erebus-labs/blocks-o-code/docs/Test Plans/Hardware-3.pdf

Test Case Name: | Programmer Breakout Connectivity | Test ID: | ABC-Hardware-03
Description: | Verify connectivity of external programmer breakout. | Type: | Black box

Tester Information:
Name of Tester: | | | Date:
Harware Ver: | | BlockBoard v2.2 | Time:
Setup: | | A fully populated programmer breakout. A digital multimeter will be required.
| Action | Expected Result | Pass | Fail | Comments
1 | Measure between header pin 1 and connector pin 3. | Electrical connection present.
2 | Measure between header pin 2 and connector pin 7. | Electrical connection present.
3 | Measure between header pin 3 and connector pin 8. | Electrical connection present.
4 | Measure between header pin 4 and connector pin 9. | Electrical connection present.
5 | Measure between header pin 5 and connector pin 1. | Electrical connection present.
6 | Measure between header pin 6 and connector pin 6. | Electrical connection present.

Overall test result

Ste

p

Test Writer: Daniel Frister
