erebus-labs/blocks-o-code/images/BlockBoard2.png

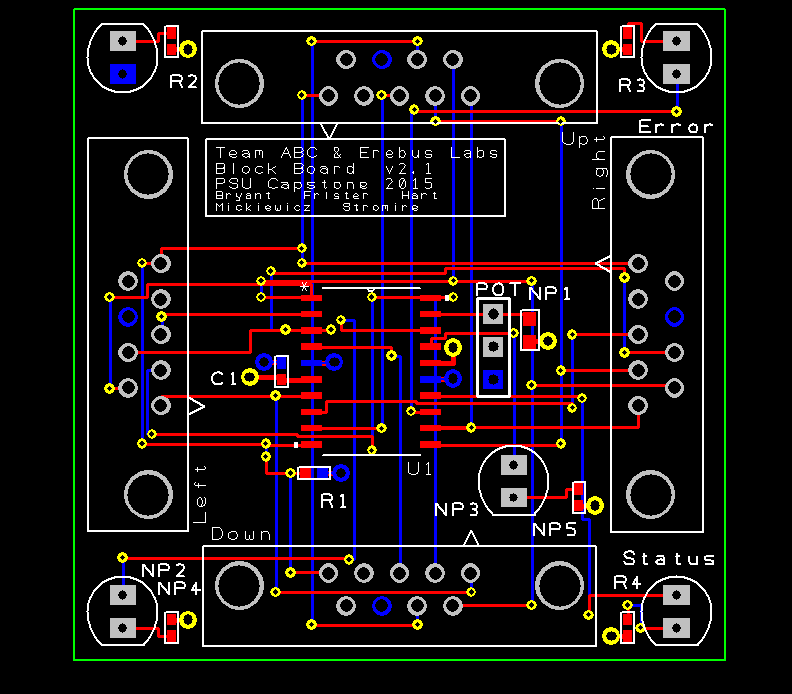
images/BlockBoard2.png
