erebus-labs/blocks-o-code/images/blockFace_with_wheel.png

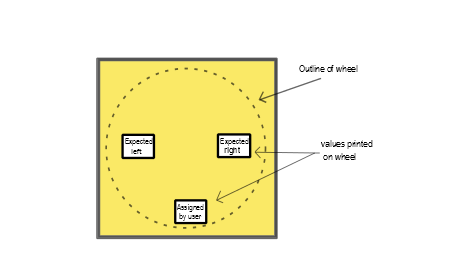
images/blockFace_with_wheel.png
