erebus-labs/blocks-o-code/images/osh.png

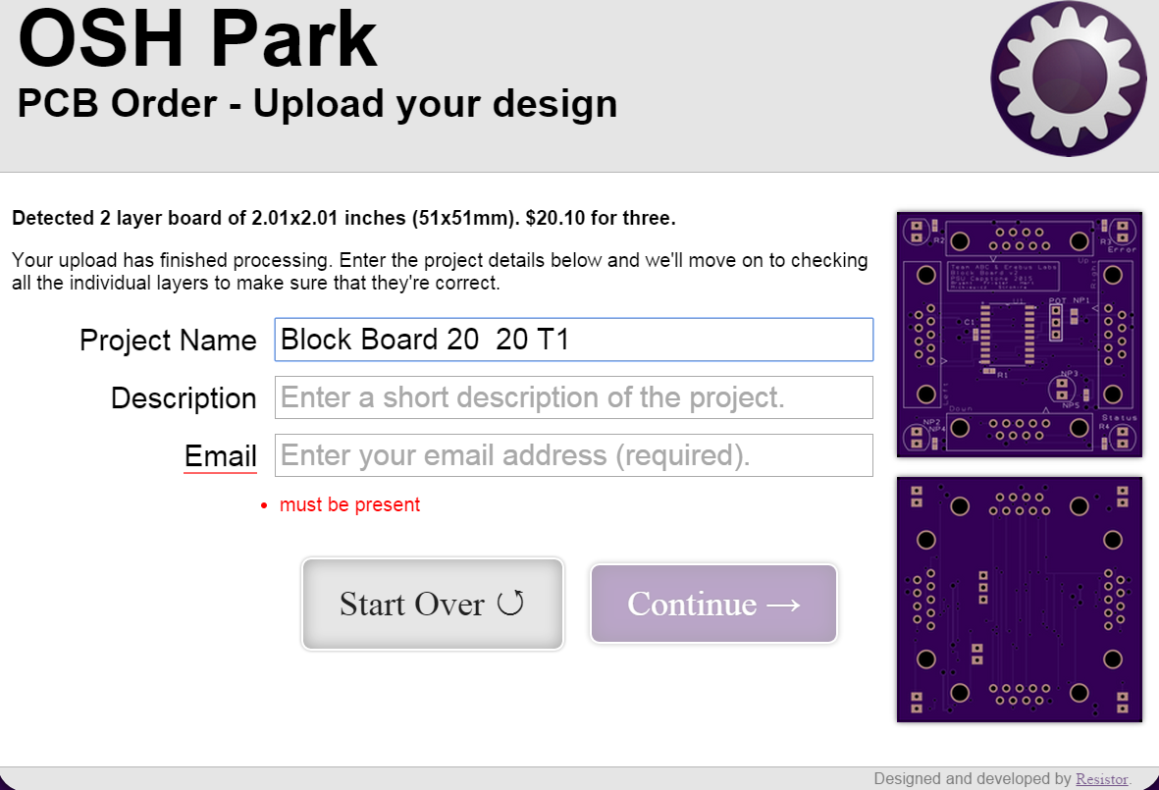
images/osh.png
