erebus-labs/blocks-o-code/docs/pdfs/BlockBoard - Schematic.pdf

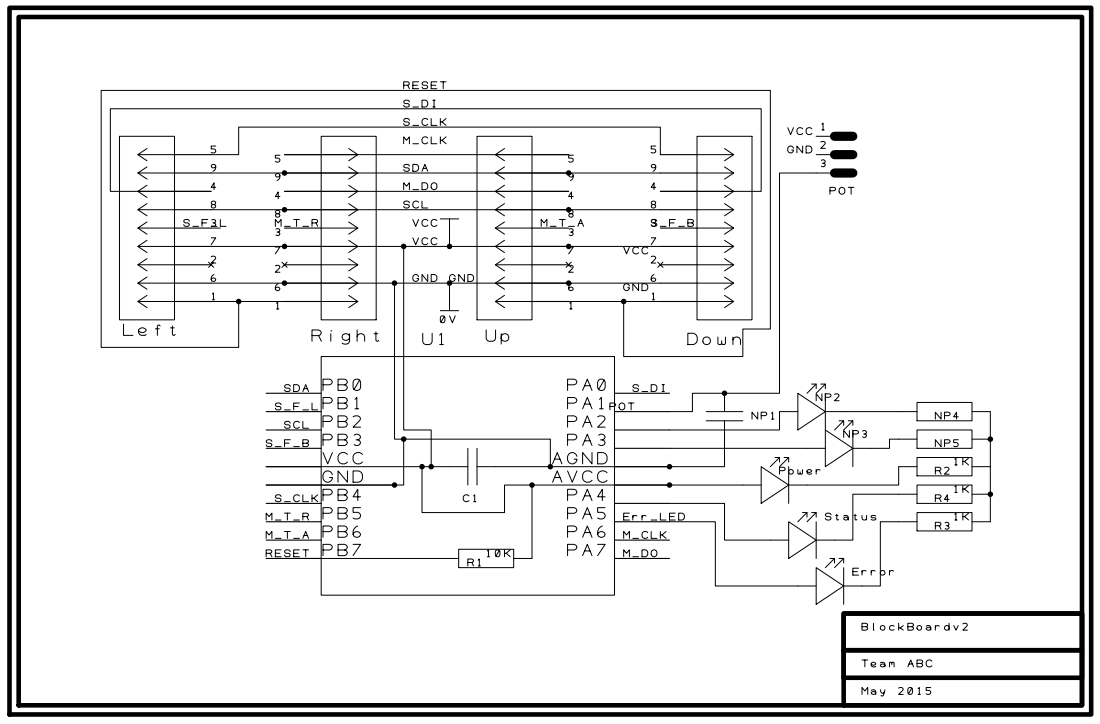
[picture p45: page 1]
