erebus-labs/blocks-o-code/docs/pdfs/BlockBoard - PCB.pdf

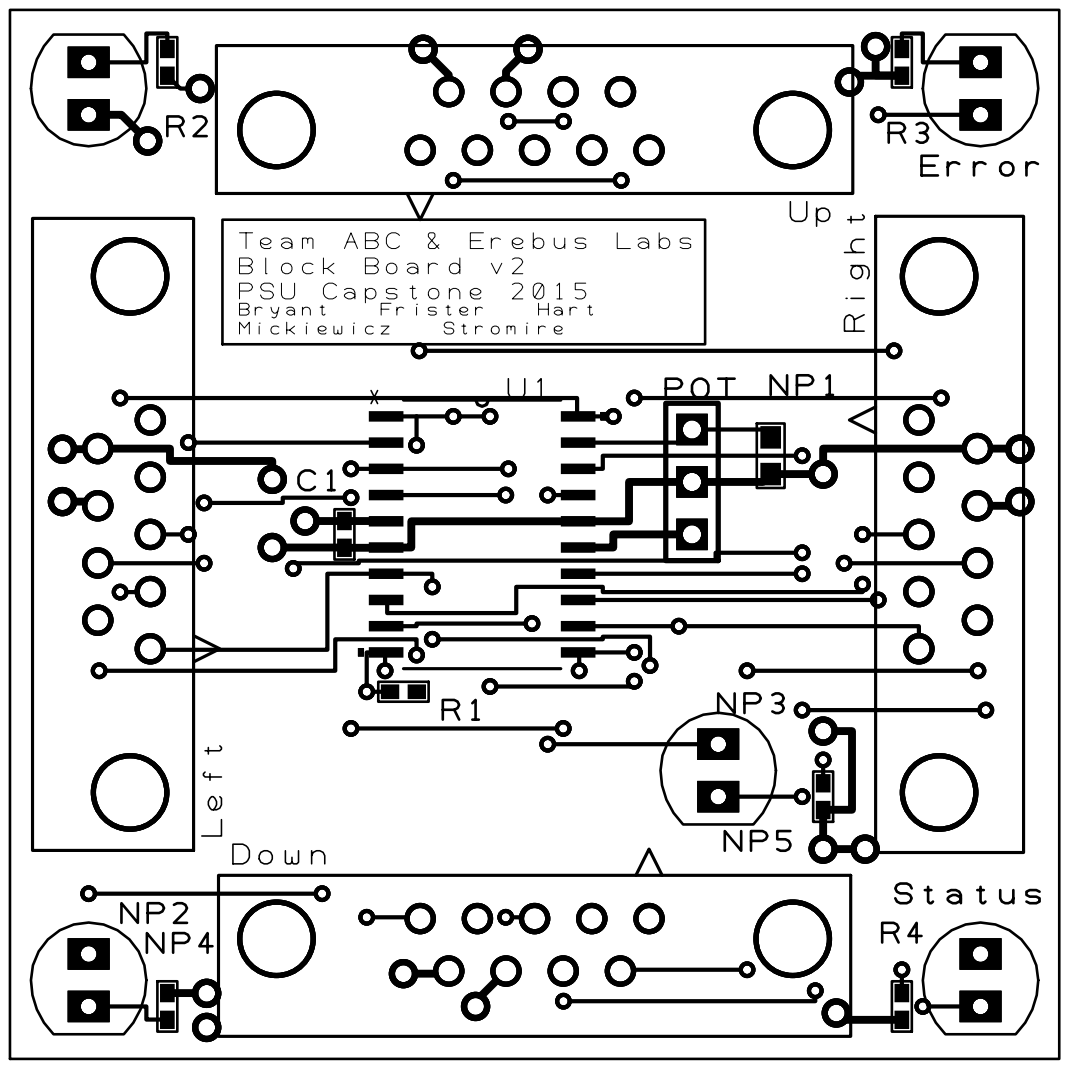
[picture p46: page 1]
