erebus-labs/blocks-o-code/docs/pdfs/ABlockofCodeSchedGantt.pdf

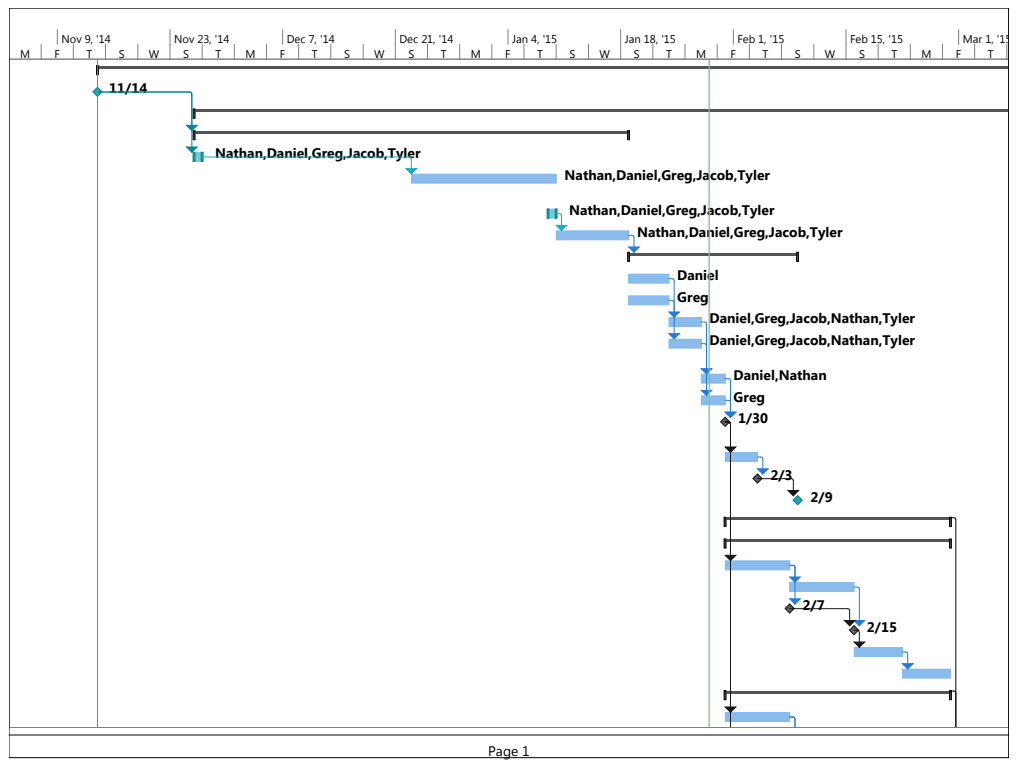
[picture p47: page 1]
Daniel,Nathan; Greg; Nov 9, '14; Nov 23, '14; Dec 7, '14; Dec 21, '14; Jan 4, '15; Jan 18, '15; Feb 1, '15; Feb 15, '15; Mar 1, '15; Page 1

Nathan,Daniel,Greg,Jacob,Tyler

Daniel
Greg
Daniel,Greg,Jacob,Nathan,Tyler

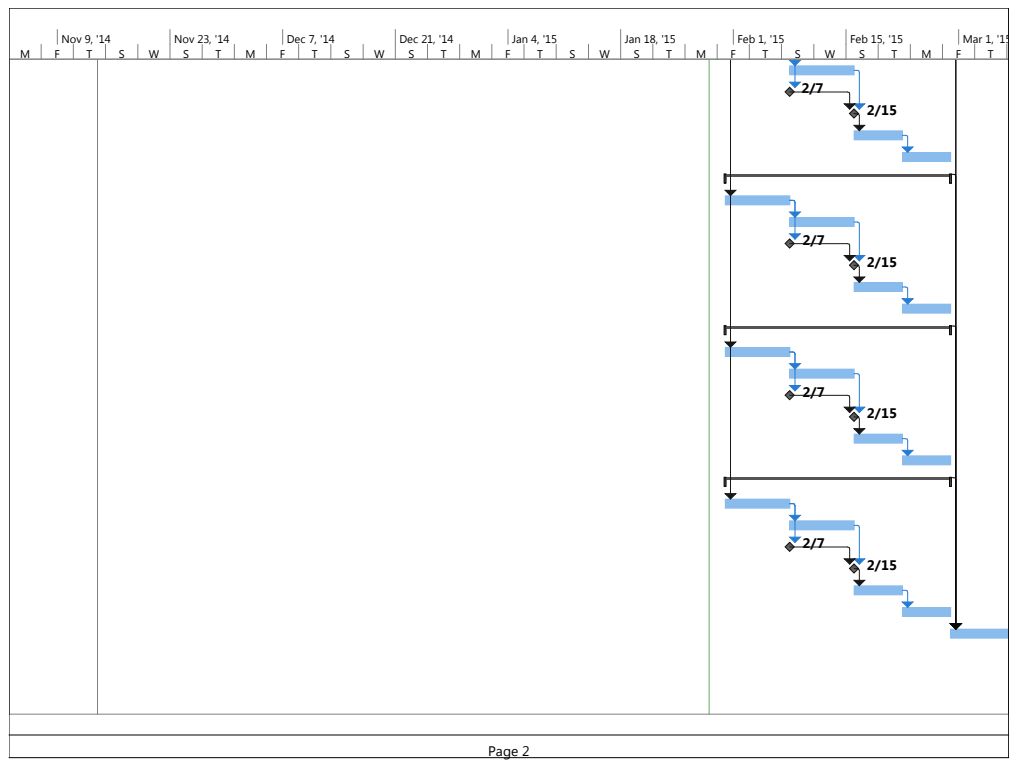
[picture p48: page 2]
Nov 9, '14; Nov 23, '14; Dec 7, '14; Dec 21, '14; Jan 4, '15; Jan 18, '15; Feb 1, '15; Feb 15, '15; Mar 1, '15; Page 2

M | F | T | S | W | S | T | M | F | T | S | W | S | T | M | F | T | S | W | S | T | M | F | T | S | W | S | T | M | F | T
Nov 9, '14 | Nov 23, '14 | Dec 7, '14 | Dec 21, '14 | Jan 4, '15 | Jan 18, '15 | Feb 1, '15 | Feb 15, '15 | Mar 1, '15

### Page 3

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

### Page 4

S | W | S | T | M | F | T | S | W | S | T | M | F | T | S | W | S | T | M | F | T | S | W | S | T | M | F | T | S | W | S
Mar 15, '15 | Mar 29, '15 | Apr 12, '15 | Apr 26, '15 | May 10, '15 | May 24, '15 | Jun 7, '15 | Jun 21, '15 | Jul 5, '15

### Page 5

### Daniel,Greg,Jacob,Nathan,Tyler

### Daniel,Greg,Jacob,Nathan,Tyler

### Greg

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

### Page 6

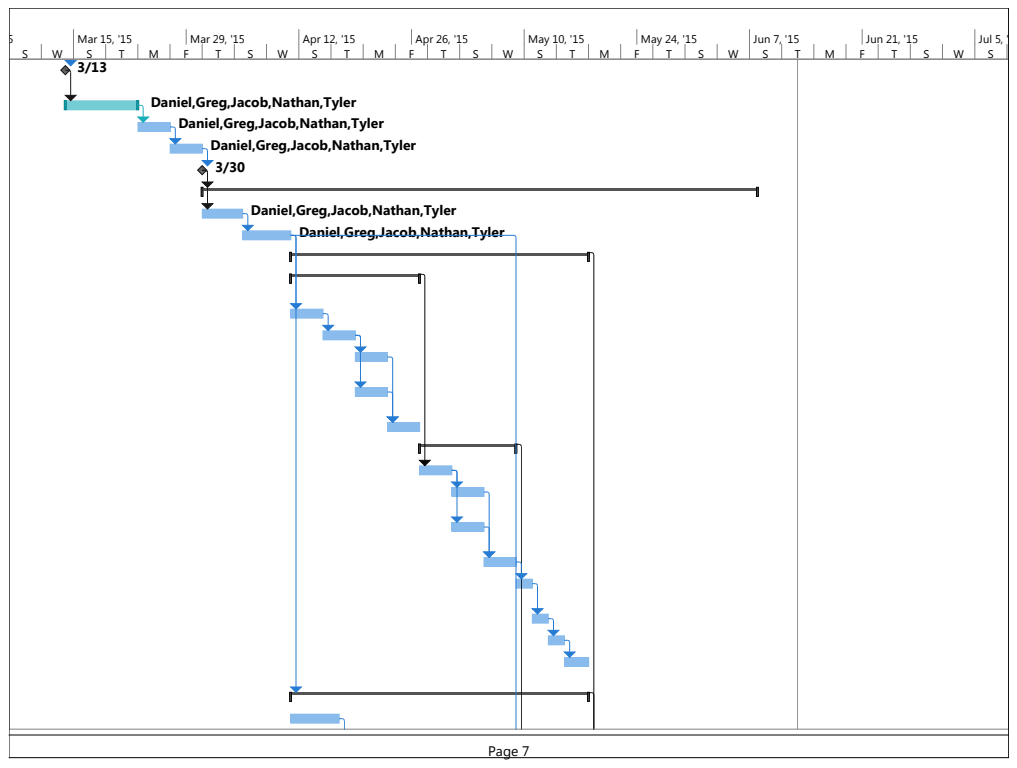
[picture p49: page 7]
Mar 15, '15; Mar 29, '15; Apr 12, '15; Apr 26, '15; May 10, '15; May 24, '15; Jun 7, '15; Jun 21, '15; Jul 5, '15; Page 7

Daniel,Greg,Jacob,Nathan,Tyler

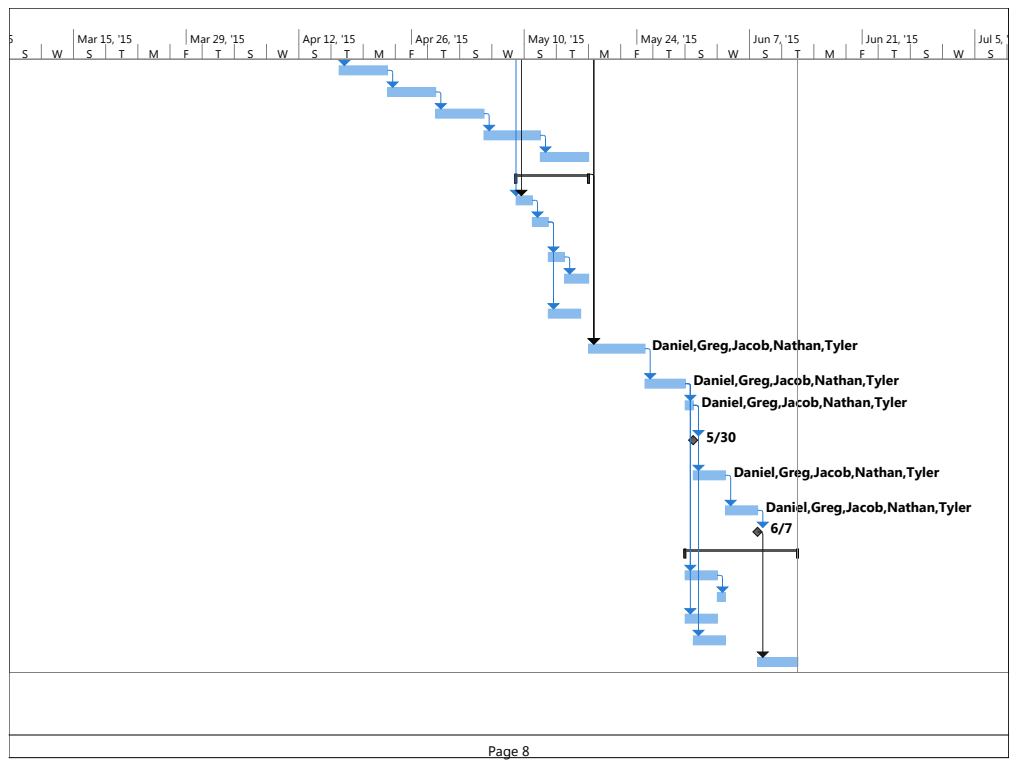
[picture p50: page 8]
Mar 15, '15; Mar 29, '15; Apr 12, '15; Apr 26, '15; May 10, '15; May 24, '15; Jun 7, '15; Jun 21, '15; Jul 5, '15; Page 8

Daniel,Greg,Jacob,Nathan,Tyler
