erebus-labs/blocks-o-code/dev/uC/LEDs/main.c

//
// Integrated Daisy Chain and I2C for A Block of Code project
//

#include "abc_daisy.h"
#include "i2c_slave.h"

static void initIO(void);
static void startupSequence(void);

int main(void) {
	
	// initialization
	initIO();
	startupSequence();
	startupSequence();
	_delay_ms(100);
	
	// spin until position received from connected block (or BBB)
	uint8_t addr = waitForVector();
	
	// add offset to show up in BBB scan
	addr += 10;
	
	// assign received vector to i2c initialization
	setup_i2c(addr, 36, 0, 3);
	sei();
	
	// continuously poll i2c for commands
	while (loop_i2c()) {
		_delay_ms(200);
		TOGGLE_STATUS;
	}
	return 0; // never reached
}


void initIO(void) {
	// set output pins
#ifdef MCU_2313
	DDRA |= _BV(PD0);
	DDRA |= _BV(PD1);
	DDRA |= _BV(PD2);
	DDRA |= _BV(PD3);
	DDRA |= _BV(STATUS_LED);
	DDRA |= _BV(ERROR_LED);
#endif
#ifdef MCU_461
	DDRA |= _BV(PA2);
	DDRA |= _BV(PA3);
	DDRA |= _BV(PA4);
	DDRA |= _BV(PA5);
	DDRA |= _BV(STATUS_LED);
	DDRA |= _BV(ERROR_LED);
#endif
}

void startupSequence(void) {
#ifdef MCU_2313
	for(int i = 0; i < 4; ++i){
		_delay_ms(25);
		PORTD |= _BV(PD0 + i);
	}
	for(int i = 0; i < 4; ++i){
		_delay_ms(25);
		PORTD &= ~_BV(PD0 + i);
	}
#endif
#ifdef MCU_461
	PORTA |= _BV(PA2);
	_delay_ms(25);
	PORTA |= _BV(PA3);
	_delay_ms(25);
	PORTA |= _BV(PA4);
	_delay_ms(25);
	PORTA |= _BV(PA5);
	_delay_ms(25);
	PORTA &= ~_BV(PA2);
	_delay_ms(25);
	PORTA &= ~_BV(PA3);
	_delay_ms(25);
	PORTA &= ~_BV(PA4);
	_delay_ms(25);
	PORTA &= ~_BV(PA5);
	_delay_ms(25);
	PORTA &= 0b11000000;
#endif
}
