erebus-labs/blocks-o-code/src/controller/abc/interpreter/src/globals.h

/****************************************
****         A Block of Code         ****
*****************************************

Parsing Emulator for A Block of Code
* Greg's proposal for syntax/symantics

(C)2014-2015 Erubus Labs
* For internal use only (subject to change)

****************************************/

/// \file globals.h
/// \brief A nice place to put stuff

#ifndef ABC_GLOBALS_H
#define ABC_GLOBALS_H

/* Macros ******************************/
#ifdef PRINTDEBUGINFO
#define DEBUG(...) fprintf(stderr, ">>> " __VA_ARGS__);
#else
#define DEBUG(...) ;
#endif

/* Globals *****************************/
extern double globals[];
extern FILE* g_source_file;
extern int g_interactive_quit;

void g_reset_globals();

#endif
