erebus-labs/blocks-o-code/dev/BBB/abc_global.py

# abc_global.py

from Adafruit_I2C import Adafruit_I2C

class Commands:
    (
    ReadData,
    SendVertical,
    SendHorizontal,
    StatusLedOn,
    StatusLedBlink,
    StatusLedOff,
    ErrorLedOn,
    ErrorLedBlink,
    ErrorLedOff,
    Reset,
    AuxiliaryRead
    ) = range(11)


class ABC_Global_Bus(object):
    """docstring for ABC_Global_Bus"""
    def __init__(self):
        super(ABC_Global_Bus, self).__init__()
        f = open('/sys/devices/bone_capemgr.9/slots', 'w')
        f.write('BB-I2C1')
        try:
            f.close()
        except IOError as e:
            if e.errno != 17:
                raise

    def formatAddress(self, x, y):
        if int(x) > 7 or int(y) > 15:
            return -1
        return (int(x) & 7) | ((int(y) & 15) << 3)

    # returns function value stored in the block's function register
    def serviceCommand(self, x, y, i2c_busnum=2, register=0):
        return Adafruit_I2C(self.formatAddress(x, y), busnum=i2c_busnum).readU8(register)

    def readData(self, x, y, i2c_busnum=2):
        return self.serviceCommand(x, y, i2c_busnum, Commands.ReadData)

    def sendVertical(self, x, y, i2c_busnum=2):
        return self.serviceCommand(x, y, i2c_busnum, Commands.SendVertical)

    def sendHorizontal(self, x, y, i2c_busnum=2):
        return self.serviceCommand(x, y, i2c_busnum, Commands.SendHorizontal)

    def statusLedOn(self, x, y, i2c_busnum=2):
        return self.serviceCommand(x, y, i2c_busnum, Commands.StatusLedOn)

    def statusLedBlink(self, x, y, i2c_busnum=2):
        return self.serviceCommand(x, y, i2c_busnum, Commands.StatusLedBlink)

    def statusLedOff(self, x, y, i2c_busnum=2):
        return self.serviceCommand(x, y, i2c_busnum, Commands.StatusLedOff)

    def errorLedOn(self, x, y, i2c_busnum=2):
        return self.serviceCommand(x, y, i2c_busnum, Commands.ErrorLedOn)

    def errorLedBlink(self, x, y, i2c_busnum=2):
        return self.serviceCommand(x, y, i2c_busnum, Commands.ErrorLedBlink)

    def errorLedOff(self, x, y, i2c_busnum=2):
        return self.serviceCommand(x, y, i2c_busnum, Commands.ErrorLedOff)

    def reset(self, x, y, i2c_busnum=2):
        return self.serviceCommand(x, y, i2c_busnum, Commands.Reset)

    def auxiliaryRead(self, x, y, i2c_busnum=2):
        return self.serviceCommand(x, y, i2c_busnum, Commands.AuxiliaryRead)
