erebus-labs/blocks-o-code/src/controller/abc/proto_lex.py

#!/usr/bin/python

from abc_lexer import ABC_Lexer
import time
import sys


delay = 1.25

continuous = False
debug = False
stderr = True
if len(sys.argv)>1:
	if '-c' in sys.argv:
		continuous = True
	if '-debug' in sys.argv:
		debug = True
	if '-E' in sys.argv:
		stderr = False

lex = ABC_Lexer(debug)

go = True
count = 1
while go:
    #time.sleep(delay)

    #print 'Run #' + str(count)
    lex.runOnce()
    print
    count += 1

    if not continuous or count == 101:
        go = False

# 00 => No Neighbor / No Changes
# 01 => New Right Block
# 10 => New Above Block
# 11 => New Above and Right Blocks
